julienfdev/nodeYT-subscriber-counter/img/jumbo-0.101f57c4.jpg

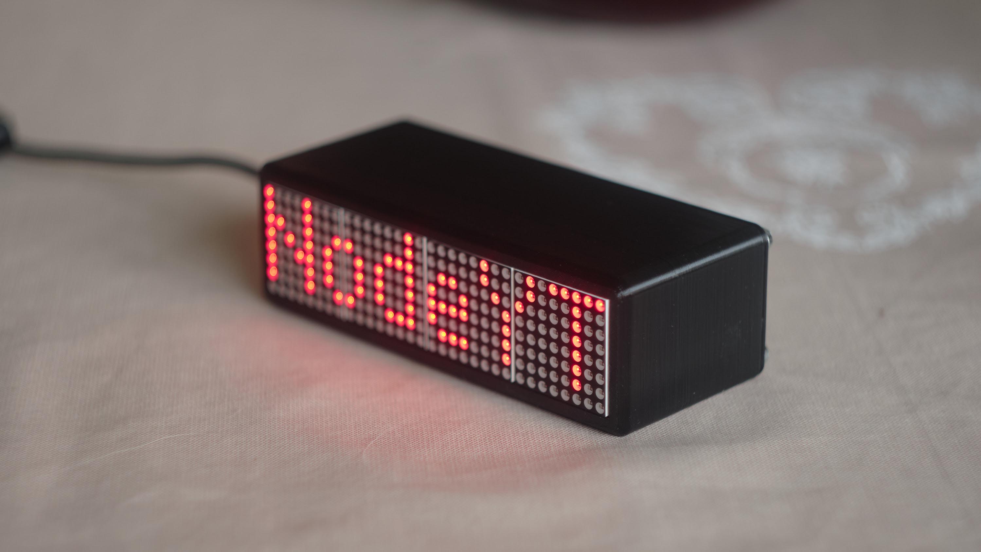
img/jumbo-0.101f57c4.jpg
