julienfdev/nodeYT-subscriber-counter/img/soft-0.41a24788.jpg

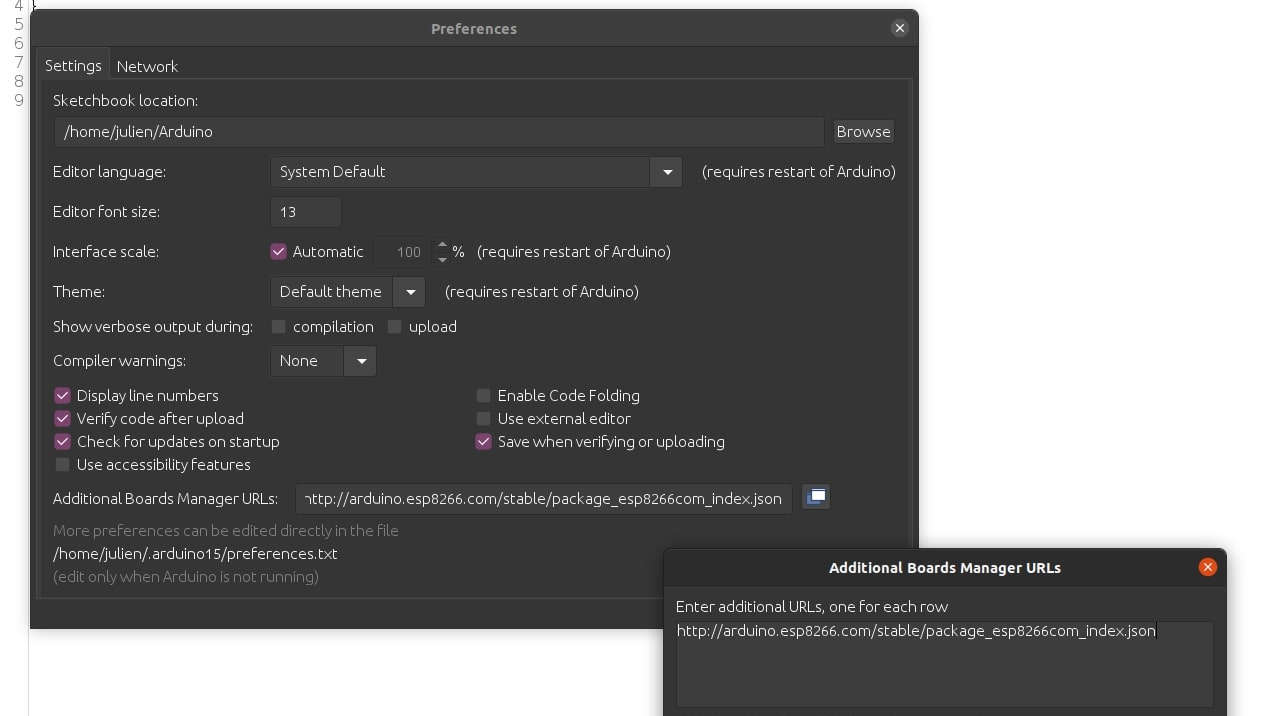
img/soft-0.41a24788.jpg
