julienfdev/nodeYT-subscriber-counter/img/soft-1.3ea3b532.jpg

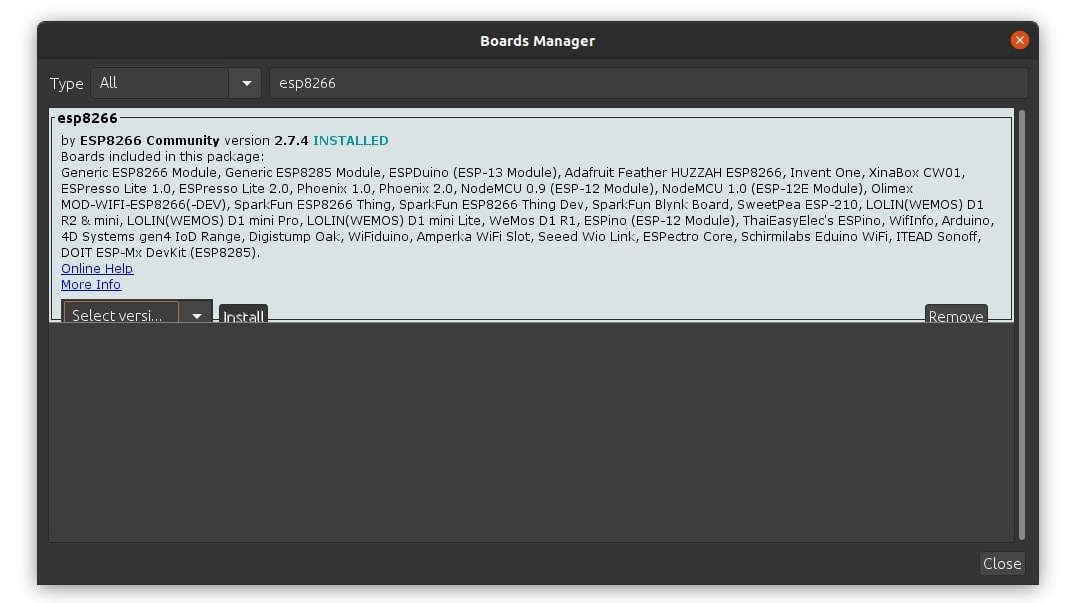
img/soft-1.3ea3b532.jpg
