julienfdev/nodeYT-subscriber-counter/img/soft-2.c622b702.jpg

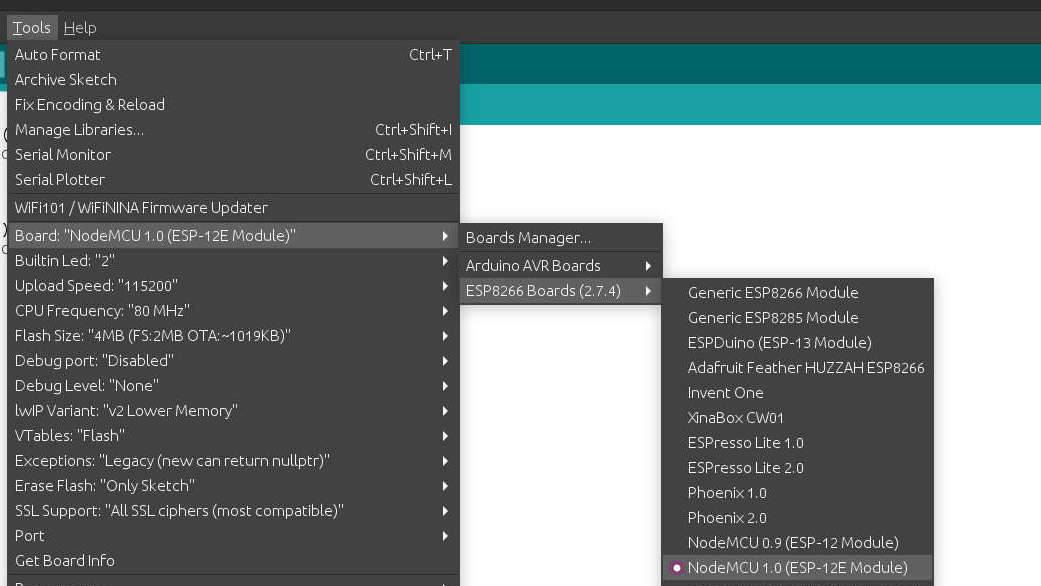
img/soft-2.c622b702.jpg
