julienfdev/nodeYT-subscriber-counter/img/soft-3.02766e15.jpg

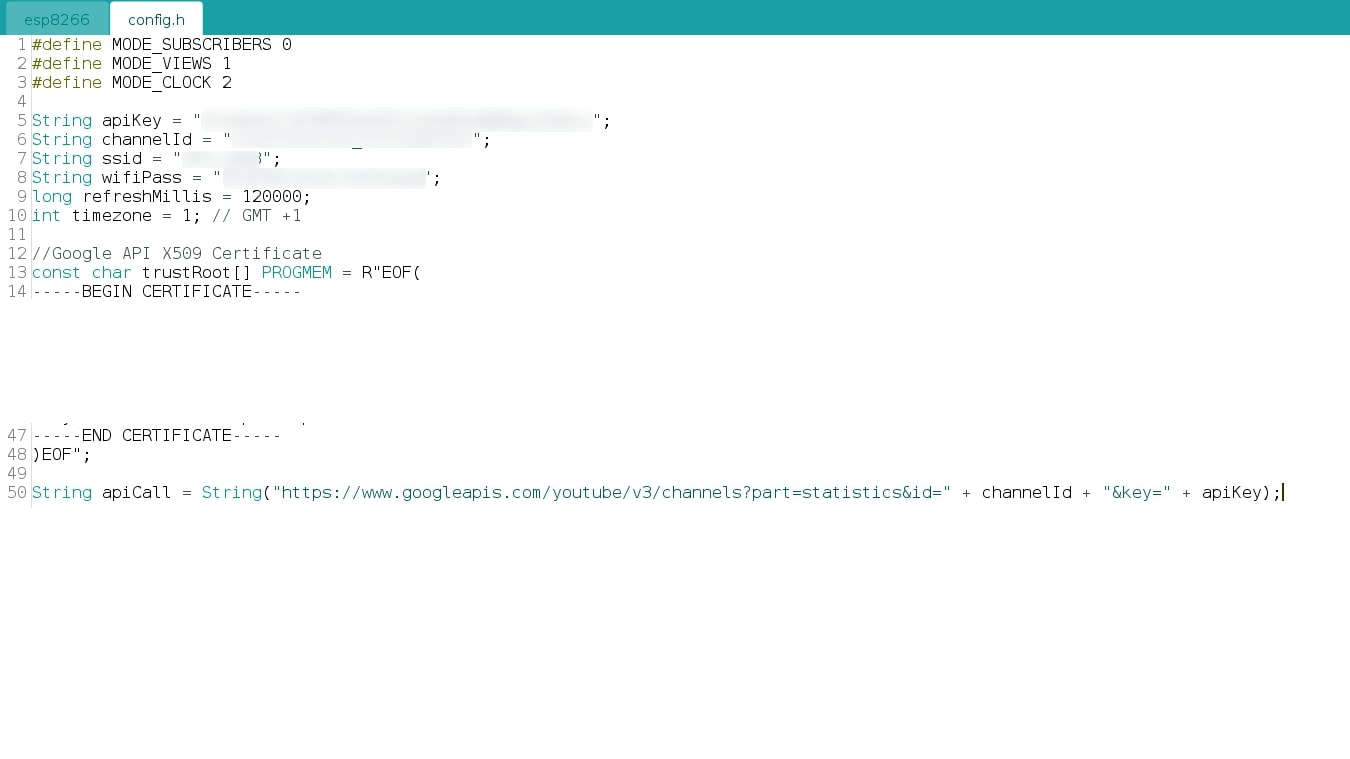
img/soft-3.02766e15.jpg
