julienfdev/nodeYT-subscriber-counter/img/bom.5f0602e5.jpg

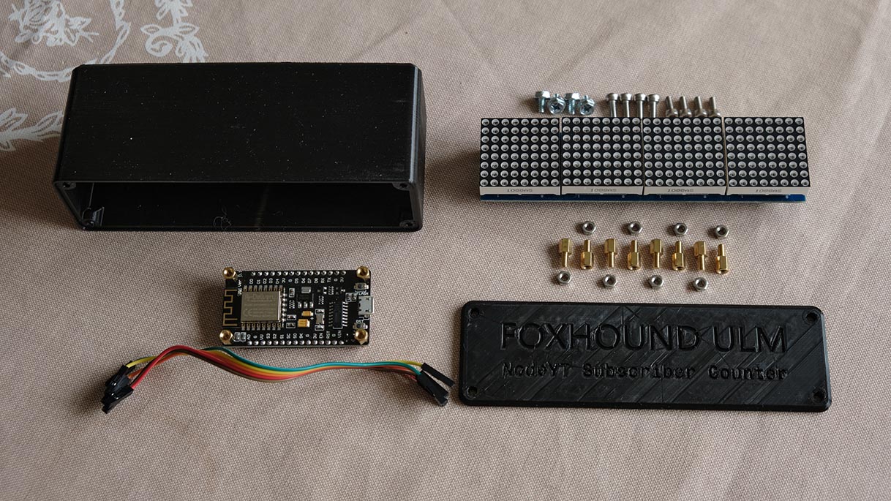
img/bom.5f0602e5.jpg
