julienfdev/nodeYT-subscriber-counter/img/howto-0.f9461eb2.jpg

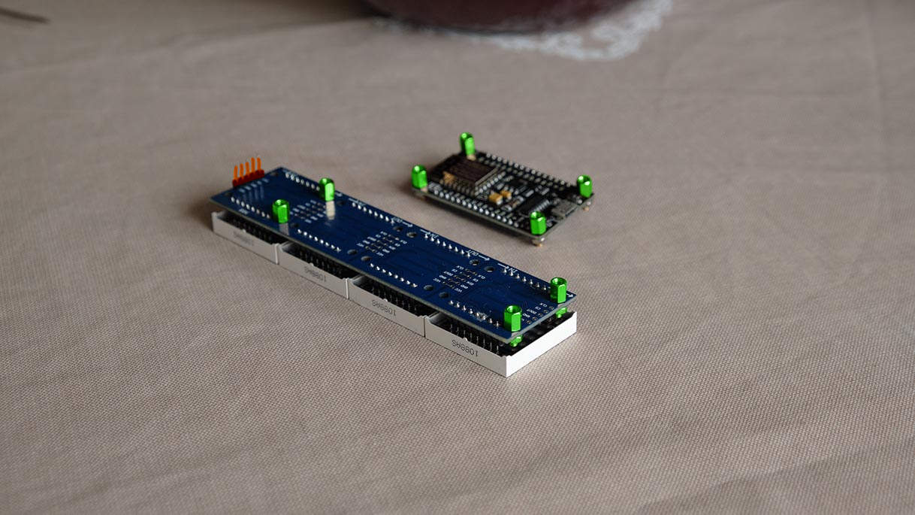
img/howto-0.f9461eb2.jpg
