julienfdev/nodeYT-subscriber-counter/img/howto-1.9da7182d.jpg

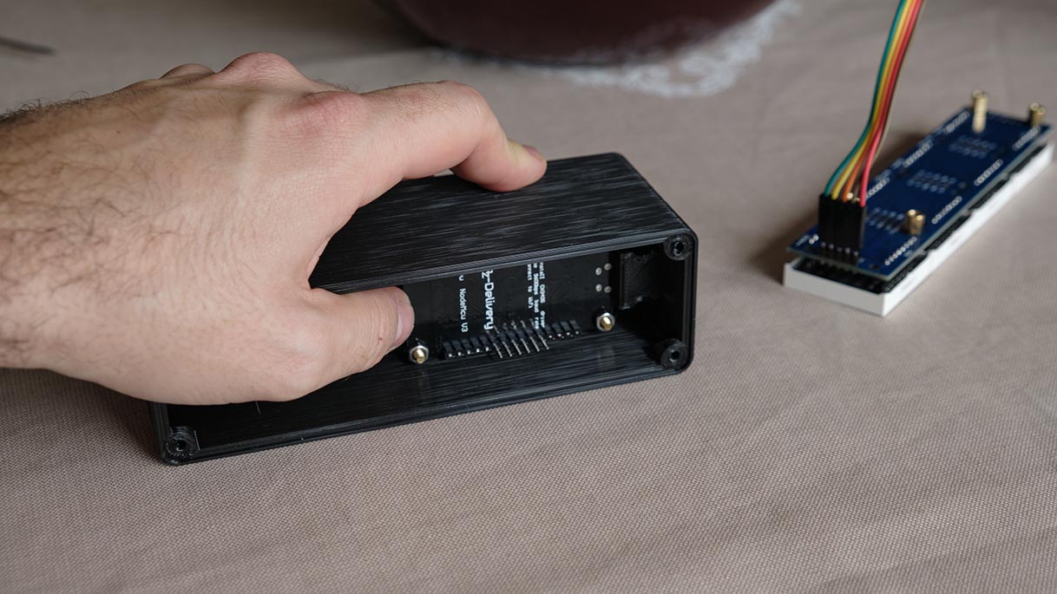
img/howto-1.9da7182d.jpg
