julienfdev/nodeYT-subscriber-counter/img/howto-2.d3725dab.jpg

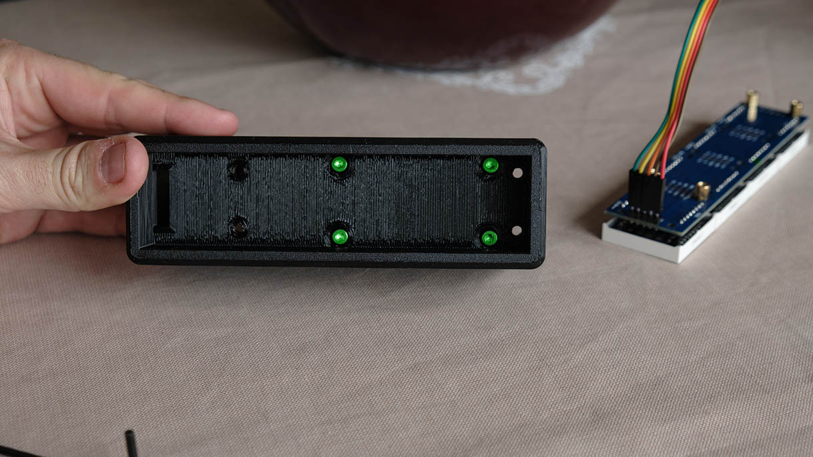
img/howto-2.d3725dab.jpg
