julienfdev/nodeYT-subscriber-counter/img/howto-3.b06c6fcf.jpg

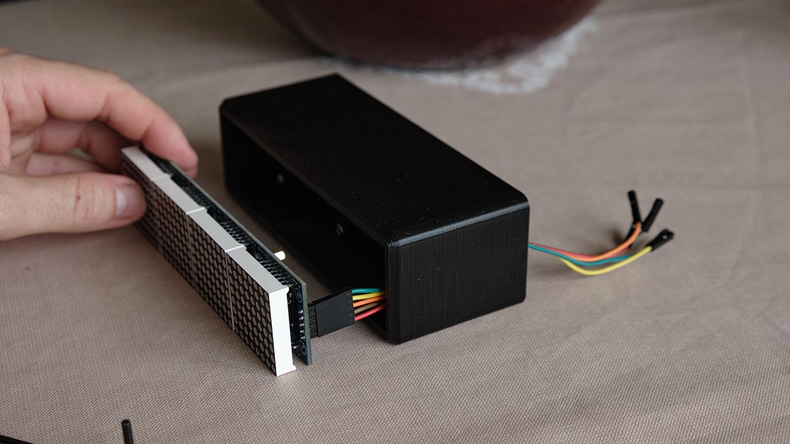
img/howto-3.b06c6fcf.jpg
