julienfdev/nodeYT-subscriber-counter/img/howto-4.013137a0.jpg

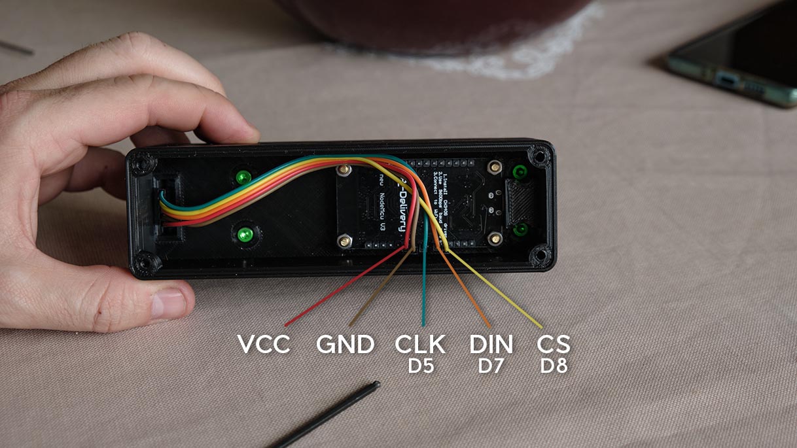
img/howto-4.013137a0.jpg
